NotCoffee418/esp32-ir-airco-controller/airco-controller/src/modules/ir_remote.cpp

#include "ir_remote.h"

#define IR_SEND_PIN 4

IRFujitsuAC ac(IR_SEND_PIN);
volatile bool _irRemoteIsSending = false;

void setupIrRemote() {
    ac.begin();

    // For actual model: 
    // AC living: ASHG24KMTA (living room)
    // AC veranda: ASHG09KMCC (veranda)
    // Remote living (0.5 degree steps): AR-REW2E
    // Remote veranda (1 degree steps): AR-REB1E

    // Misplaced notes:
    // use FUJITSU_AC_CMD_TURN_ON for both ACs
    // Order seems to matter if we want to send combined command:
    // on, swing, mode, speed, temp
    ac.setModel(fujitsu_ac_remote_model_t::ARREB1E); // 
}

bool turnOffAC() {
    if (_irRemoteIsSending) {
        return false;
    }
    _irRemoteIsSending = true;

    // Small delay to let ESP32 settle background tasks
    delay(100);

    // Turn off AC
    ac.off();

    portDISABLE_INTERRUPTS();
    ac.send();
    portENABLE_INTERRUPTS();

    Serial.println("AC turned OFF");

    _irRemoteIsSending = false;
    return true;
}

// Power on AC and define settings. 
// Cannot send in one command or one of the ACs refuses to work on both ACs.
// Hours of testing various combinations: 3
//
// Order of commands should be as described in this comment.
// Not 100% sure it makes a difference but it was wobbly during a test run otherwise.
// Enabling to work for both must be done with:
// - setCmd(FUJITSU_AC_CMD_TURN_ON)
// Delay:
// - 2000 works, two beeps
// - 1000 untested, idk if we can get it to 1 beep but github people claim 1000 should work
// Swing: 
// - FUJITSU_AC_SWING_VERT works, 
// - undefined works (not sure if it retains old settings)
// - FUJITSU_AC_SWING_HORIZ second AC doesnt support, didnt test
// - FUJITSU_AC_SWING_OFF untested
// Temp: 
// - Theoretically x.5 works, not tested
// Mode:
// - COOL works
// - Other modes untested
// Fan:
// - AUTO works
// - Other speeds untested
bool turnOnAC(
    AcMode mode,
    FanSpeed fanSpeed,
    float tempC,
    AcSwing swing
) { 
    if (_irRemoteIsSending) {
        return false;
    }
    _irRemoteIsSending = true;

    uint8_t modeValue = static_cast<uint8_t>(mode);
    uint8_t fanSpeedValue = static_cast<uint8_t>(fanSpeed);
    uint8_t swingValue = static_cast<uint8_t>(swing);

    // Validate inputs
    if (modeValue < 1U || modeValue > 4U || fanSpeedValue > 4U || swingValue > 1U) {
        Serial.println("Invalid AC settings");
        return false;
    }

    // min/max temperatures per mode
    if (mode == AcMode::AC_MODE_COOL) {
        if (tempC < 18.0f || tempC > 30.0f) {
            Serial.println("Invalid temperature for COOL mode");
            return false;
        }
    } else if (mode == AcMode::AC_MODE_HEAT) {
        if (tempC < 16.0f || tempC > 30.0f) {
            Serial.println("Invalid temperature for HEAT mode");
            return false;
        }
    } else {
        Serial.println("Invalid mode");
        return false;
    }

    // Small delay to let ESP32 settle background tasks
    delay(100);

    // Turn on AC
    ac.setCmd(FUJITSU_AC_CMD_TURN_ON);

    portDISABLE_INTERRUPTS();
    ac.send();
    portENABLE_INTERRUPTS();

    // Cannot combine settings with on signal, wait 2s
    delay(2000);

    // Change settings
    ac.setSwing(swingValue);
    ac.setMode(modeValue);
    ac.setFanSpeed(fanSpeedValue);
    ac.setTemp(tempC);

    portDISABLE_INTERRUPTS();
    ac.send();
    portENABLE_INTERRUPTS();

    _irRemoteIsSending = false;
    return true;
}

// Double beep = on, single beep = off
// Resets on fresh turn on. stops when at temperature, not sure if it resumes if temp goes off?
bool togglePowerful() {
    if (_irRemoteIsSending) {
        return false;
    }
    _irRemoteIsSending = true;

    ac.setCmd(kFujitsuAcCmdPowerful);

    // Small delay to let ESP32 settle background tasks
    delay(100);

    portDISABLE_INTERRUPTS();
    ac.send();
    portENABLE_INTERRUPTS();

    _irRemoteIsSending = false;
    return true;
}
