NotCoffee418/esp32-ir-airco-controller/airco-controller/src/diagnostic.h

#pragma once

#include <Arduino.h>

struct DiagnosticData {
    String ramUsage;
    String flashUsage;
    String uptime;
    bool wifiConnected;
    int rssi;
    float deviceTemperature;
    float sensorTemperature;
    String ssid;
    String deviceIp;
    String deviceIdentifier;
    bool isModeSwitchOnAuto;
};

void printDiagnosticData();
DiagnosticData getDiagnosticData();
