NotCoffee418/esp32-ir-airco-controller/airco-controller/src/storage/api_keys.h

#include <Arduino.h>
#include <vector>

struct GenerateApiKeyResult {
    String key;
    String error;
    bool success;
};


std::vector<String> getActiveApiKeys();
GenerateApiKeyResult generateApiKey();
bool removeApiKey(String key);
